dmwatson/nanofan_controller/images/IMG_1701.JPG

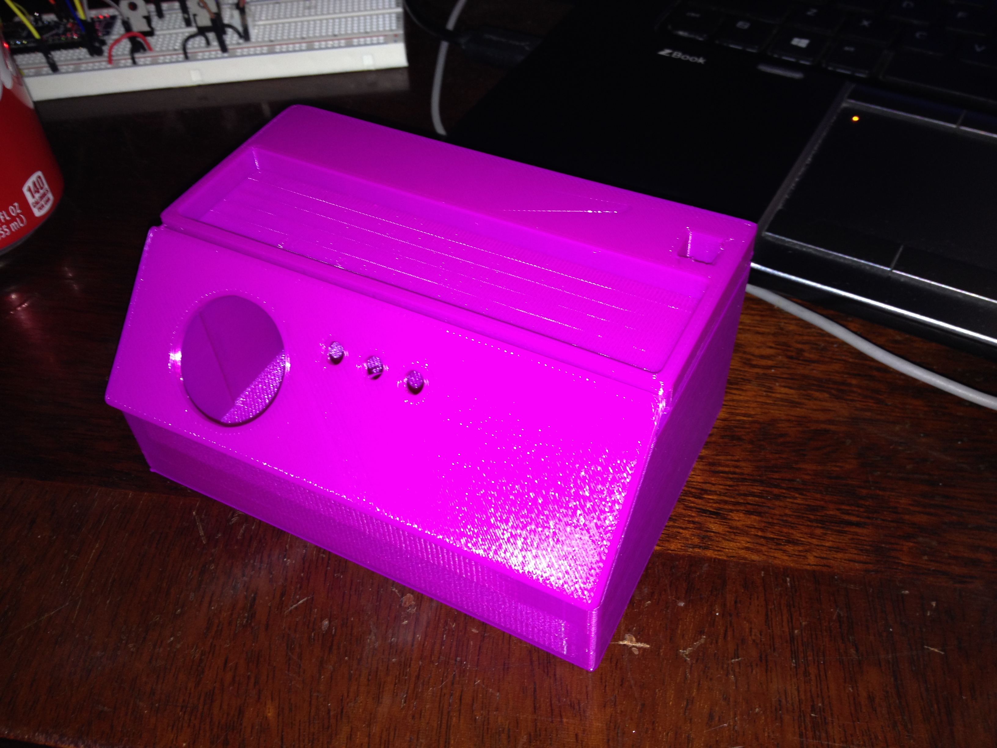
images/IMG_1701.JPG
