dmwatson/nanofan_controller/images/IMG_1703.JPG

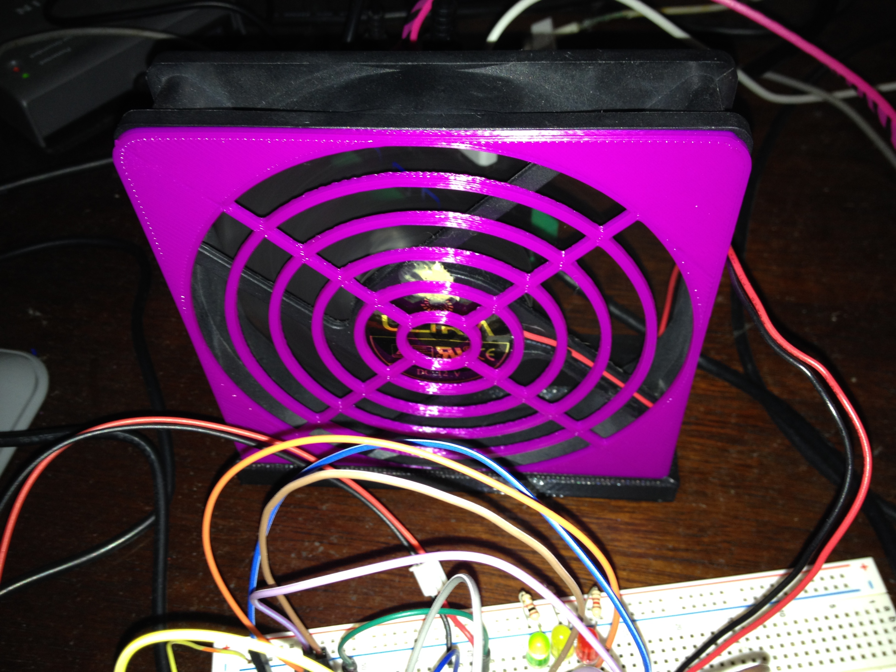
images/IMG_1703.JPG
