dmwatson/nanofan_controller/images/IMG_1707.JPG

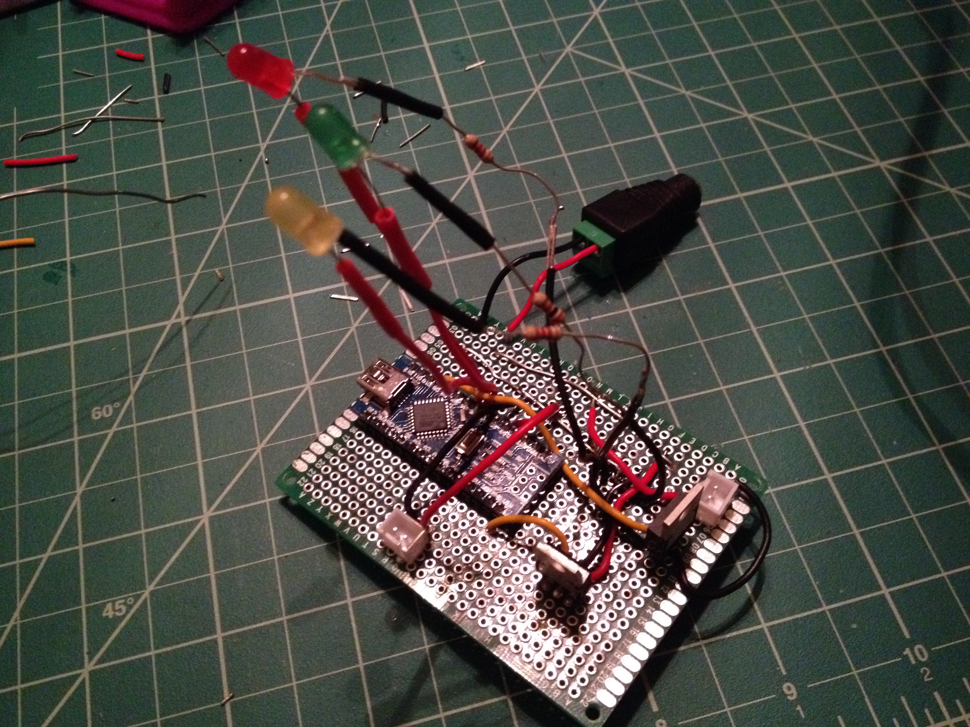
images/IMG_1707.JPG
