dmwatson/nanofan_controller/images/IMG_1711.JPG

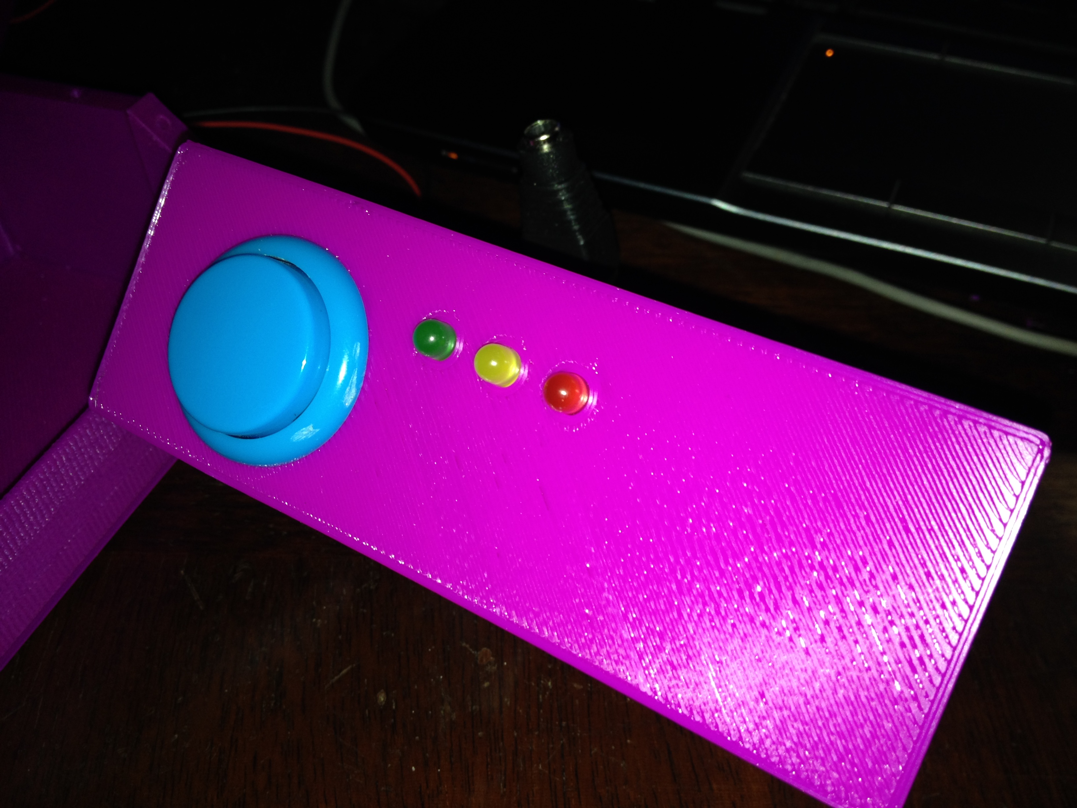
images/IMG_1711.JPG
